jeffqchen/10DIN2VGA/Pics/assembly_jumper_01.png

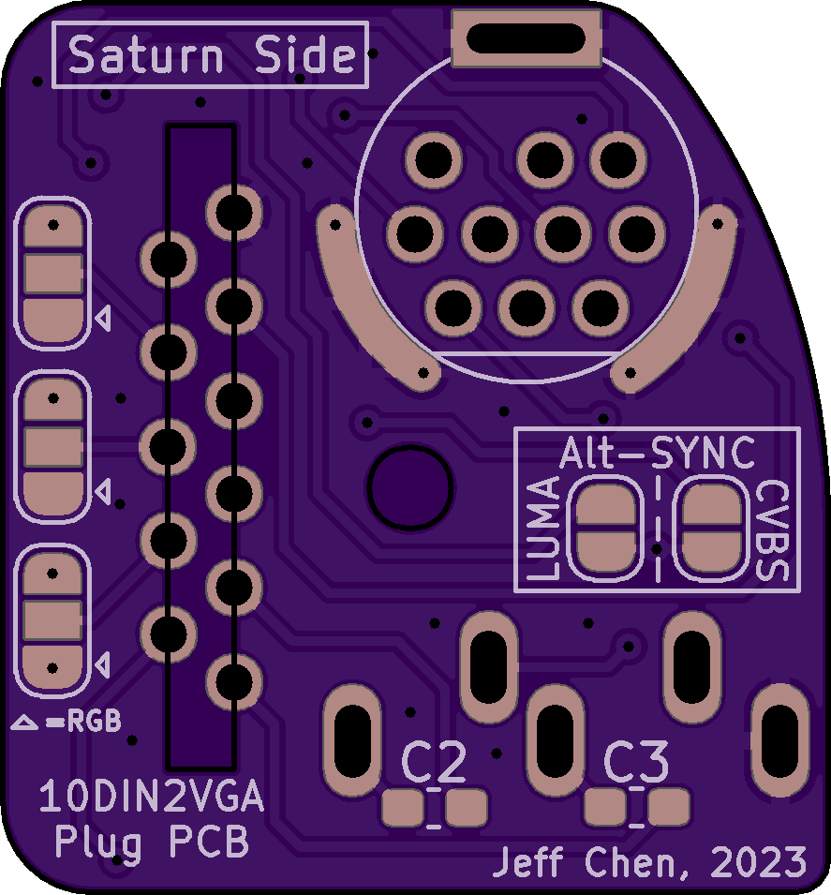
Pics/assembly_jumper_01.png
